WiseLabCMU/gridballast/Hardware/Controller/Info/Simulations/60Hz Detector/60Hz Detector Simulation - Frequency Resp.asc

C1: cap; 1µ
C2: cap; 1µ
C3: cap; 10µ
R1: res; 53k
R2: res; 134
R3: res; 13.3k
R4: res; 100k
R5: res; 100k
U1: UniversalOpamp2
U2: UniversalOpamp2
U3: UniversalOpamp2
V1: voltage; 3.3
V2: voltage; SINE(0 .2 60); AC 1
Named nets: 0, OUT, 3V3, BandFilter, ANT
.ac oct 4096 1 200
https://users.ece.cmu.edu/~agr/resources/publications/rtss-clk-13.pdf
