WiseLabCMU/gridballast/Hardware/Controller/Info/Simulations/Leak Detection Cable/Leak Detection Cable.asc

R1: res; {leak}
R2: res; {bias}
R3: res; {safety}
V1: voltage; 3.3
Named nets: 0, 3.3V, out
;op
.param LeakTypMin=1Meg
.param LeakTypMax=5Meg
.param leak=3Meg
.step param leak 7Meg 1Meg 0.1Meg
.param bias={(LeakTypMax-LeakTypMin)/2 + LeakTypMin}
Bias resistor should be around 3MOhm, since we usually operate between 1 to 5MOhm
Do note that the cable goes high-Z when completley dry.
.meas tran BiasValue param bias
;tran 0 1ms 0 0.001ms
.op
.step param safety list 0.00000001 10
