WiseLabCMU/gridballast/Hardware/Controller/Info/Simulations/MIC Amplifier and Bias/MIC Amplifier and Bias.asc

C1: cap; 1.8µ
C2: cap; 4.7µ
C3: cap; 10µ
C4: cap; 100p
I1: current; 120µ
R1: res; 12k
R2: res; 2.2k
R3: res; 10k
R4: res; 10k
R5: res; 100k
R6: res; 1.5k
U1: UniversalOpamp2
V1: voltage; 5
V2: voltage; SINE(1.8 .02 1k); AC 1
V3: voltage; 3.3
Named nets: 0, VIN, out, VDD, wire, mic, 3.3V
;tran 0 100ms 0 0.001ms
.ac oct 1Meg 1m 40k
Constitutes a low pass filter with corner at 1.33Hz.
Characteristics altered by C1
Connection
