WiseLabCMU/gridballast/Source/framework/main/include/config_server.h

/**
 * @file config_server.h
 *
 * @brief serve configuration webpage
 *
 * @author Aaron Perley <aperley@andrew.cmu.edu>
 */

#ifndef __config_server_module_h_
#define __config_server_module_h_

void config_server_run();

#endif /* __config_server_module_h_ */
